dschraitle/3dprinting/designs/abacus/20231222_124236.jpg

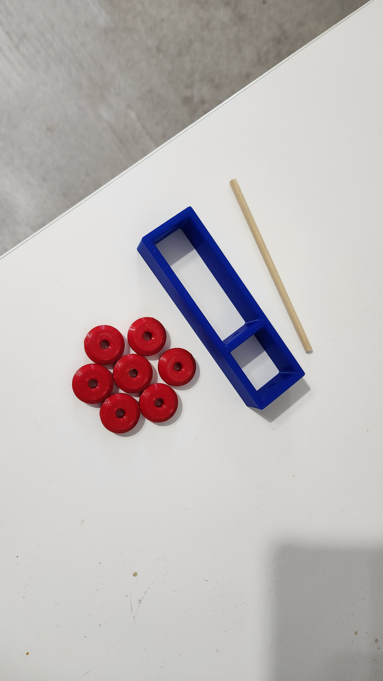
designs/abacus/20231222_124236.jpg
