dschraitle/3dprinting/designs/abacus/20231222_124335.jpg

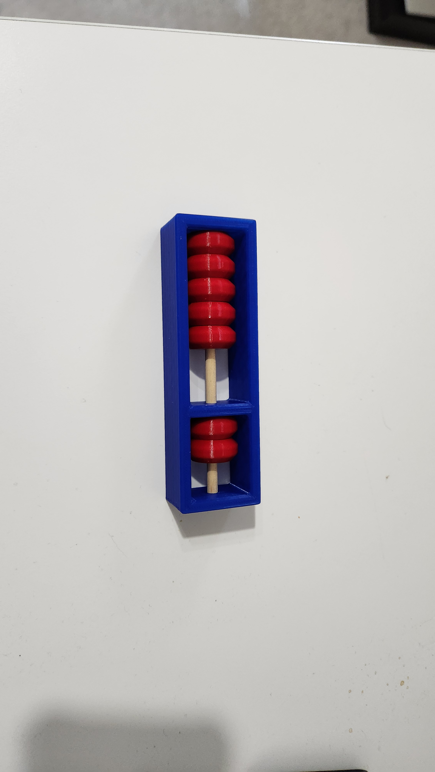
designs/abacus/20231222_124335.jpg
