dschraitle/3dprinting/designs/abacus/20231224_002757.jpg

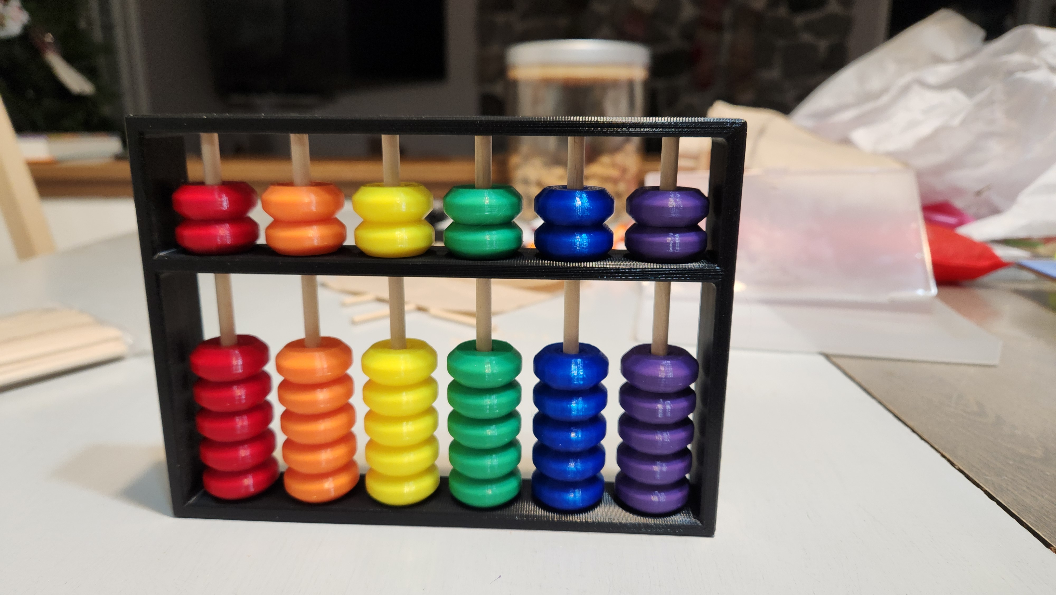
designs/abacus/20231224_002757.jpg
