dschraitle/3dprinting/designs/abacus/20231224_002802.jpg

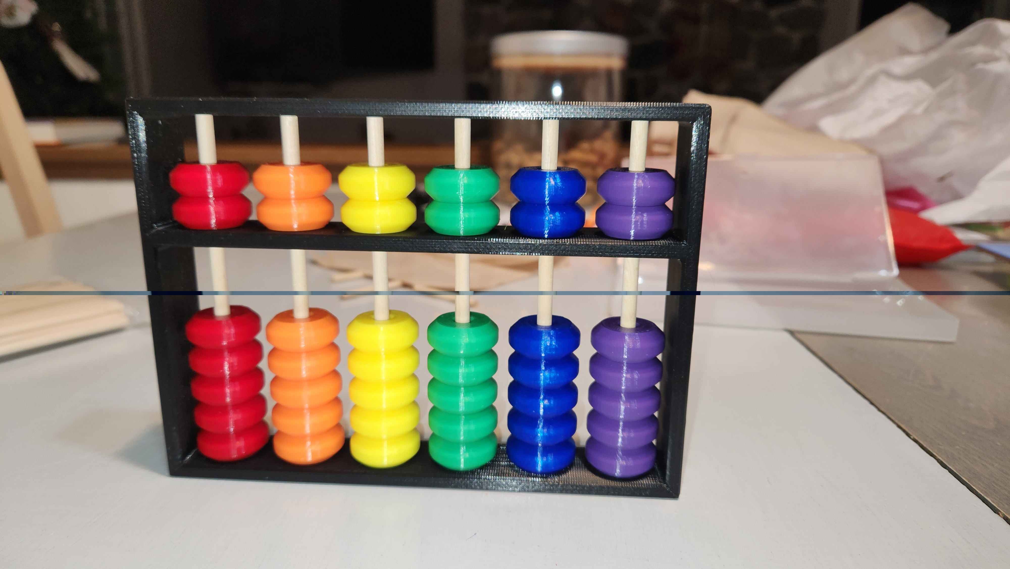
designs/abacus/20231224_002802.jpg
