dschraitle/3dprinting/designs/radio_hook/20241201_135657.jpg

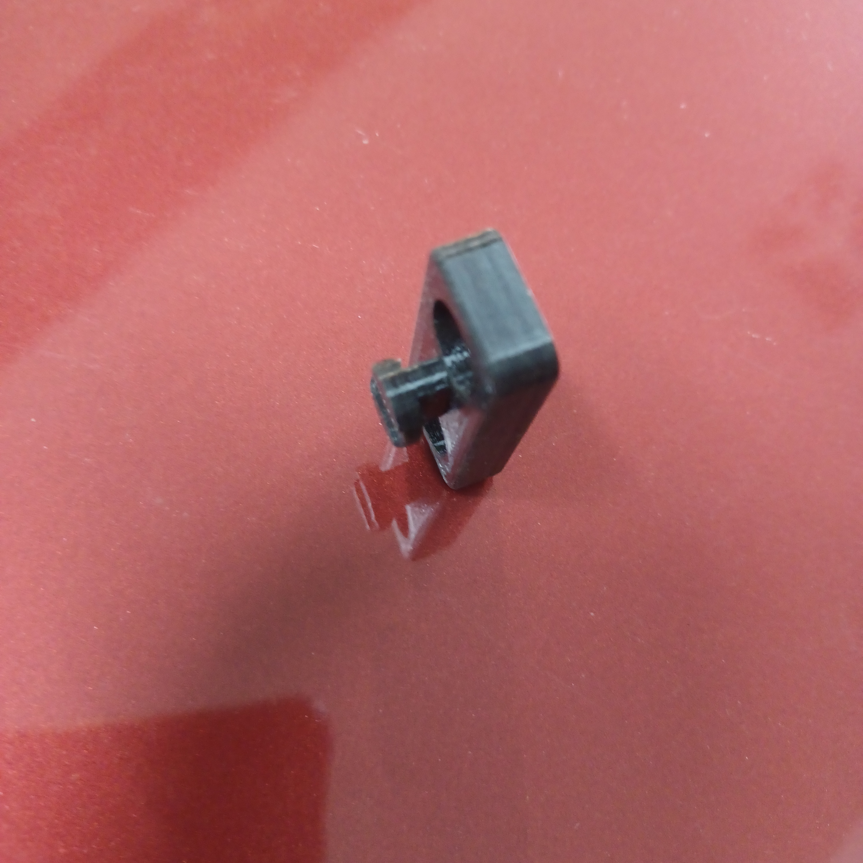
designs/radio_hook/20241201_135657.jpg
