dschraitle/3dprinting/designs/radio_hook/20241201_135714.jpg

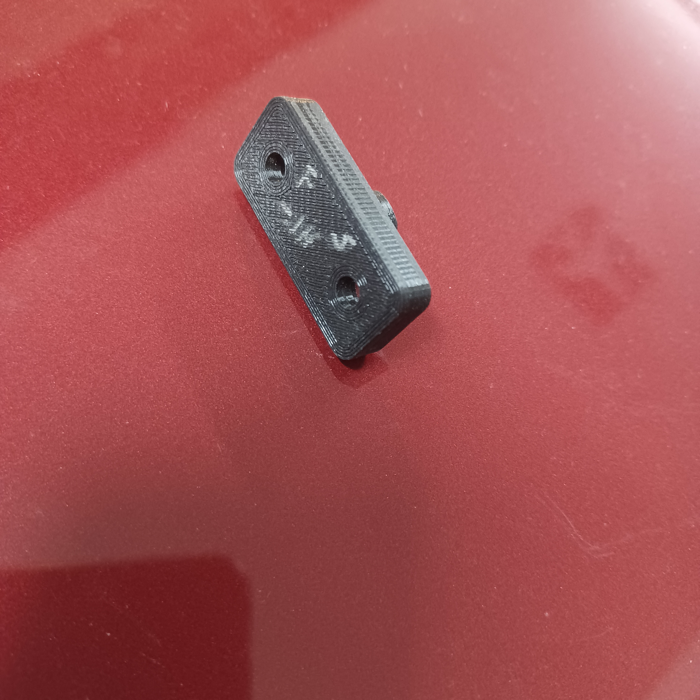
designs/radio_hook/20241201_135714.jpg
