dschraitle/3dprinting/designs/radio_hook/reference/PXL_20210319_022237038.jpg

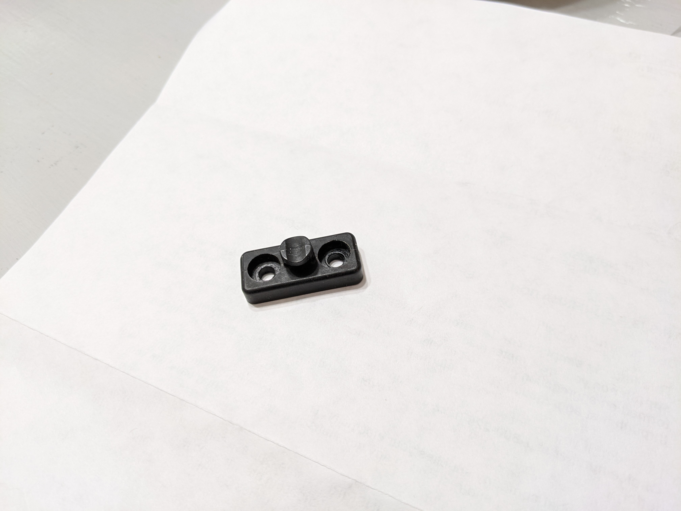
designs/radio_hook/reference/PXL_20210319_022237038.jpg
