dschraitle/3dprinting/designs/radio_hook/reference/PXL_20210319_023224287.jpg

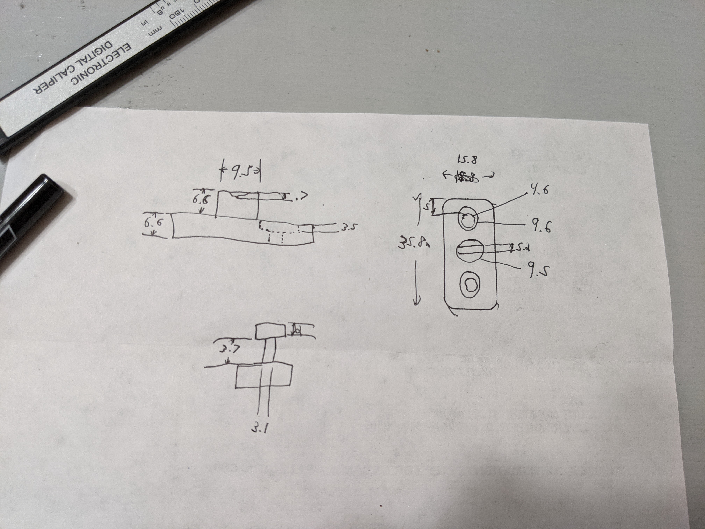
designs/radio_hook/reference/PXL_20210319_023224287.jpg
