dschraitle/3dprinting/designs/train_wheel/PXL_20201115_192025717.jpg

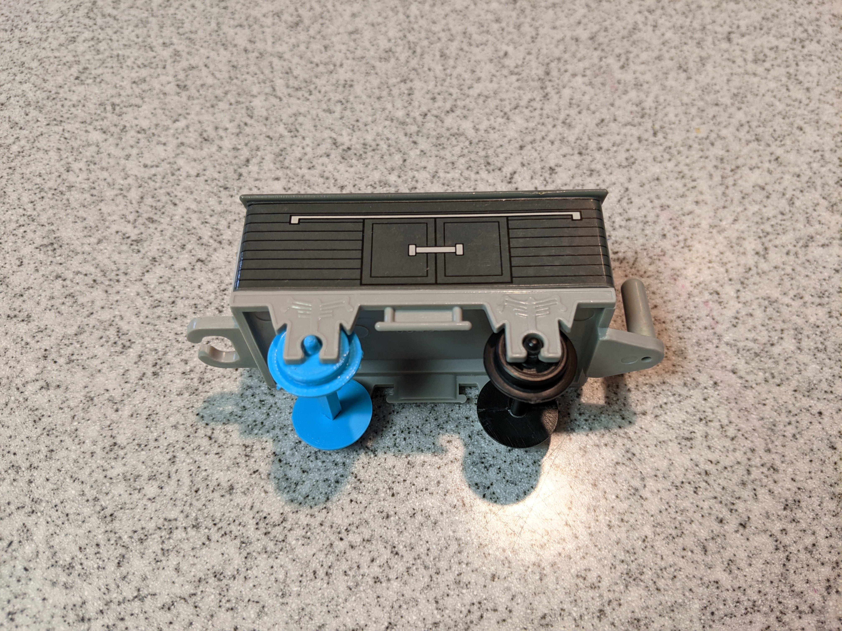
designs/train_wheel/PXL_20201115_192025717.jpg
