dschraitle/3dprinting/designs/train_wheel/PXL_20201115_192122811.jpg

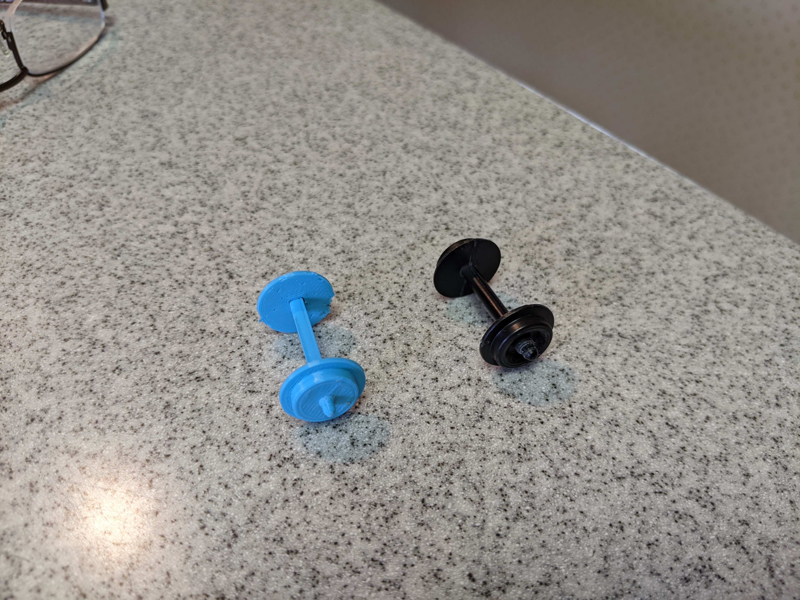
designs/train_wheel/PXL_20201115_192122811.jpg
